johnssarris/BowlPlateform/STL/Dog Bowl Plateform - Center_Top_1.stl

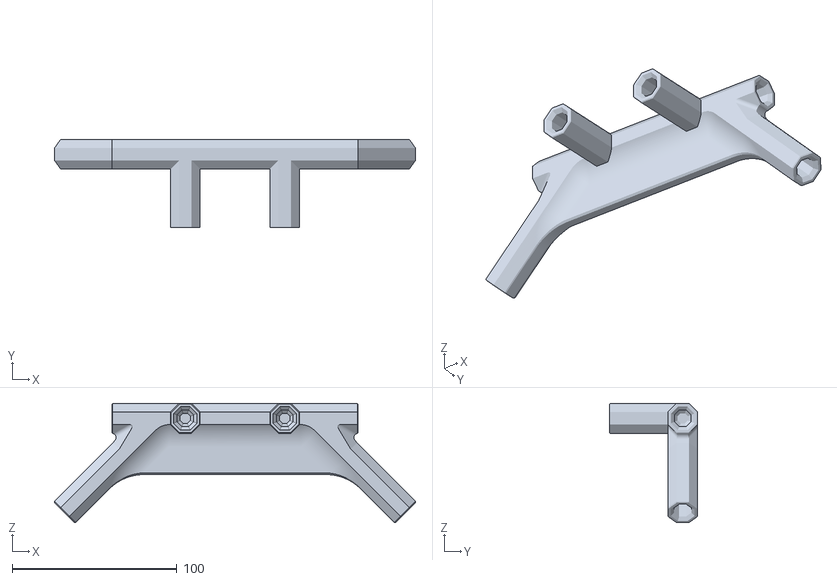
[picture p7: CAD file, 2026-05-18]
STL/Dog Bowl Plateform - Center_Top_1.stl
218.9 x 53.6 x 72.3
